rusaakkmods/dmg_boy_display/schematics/dmg_boy_display/dmg_boy_display.kicad_sch

## KiCad design schematics/dmg_boy_display/dmg_boy_display.kicad_sch (2025-08-26, an earlier design)

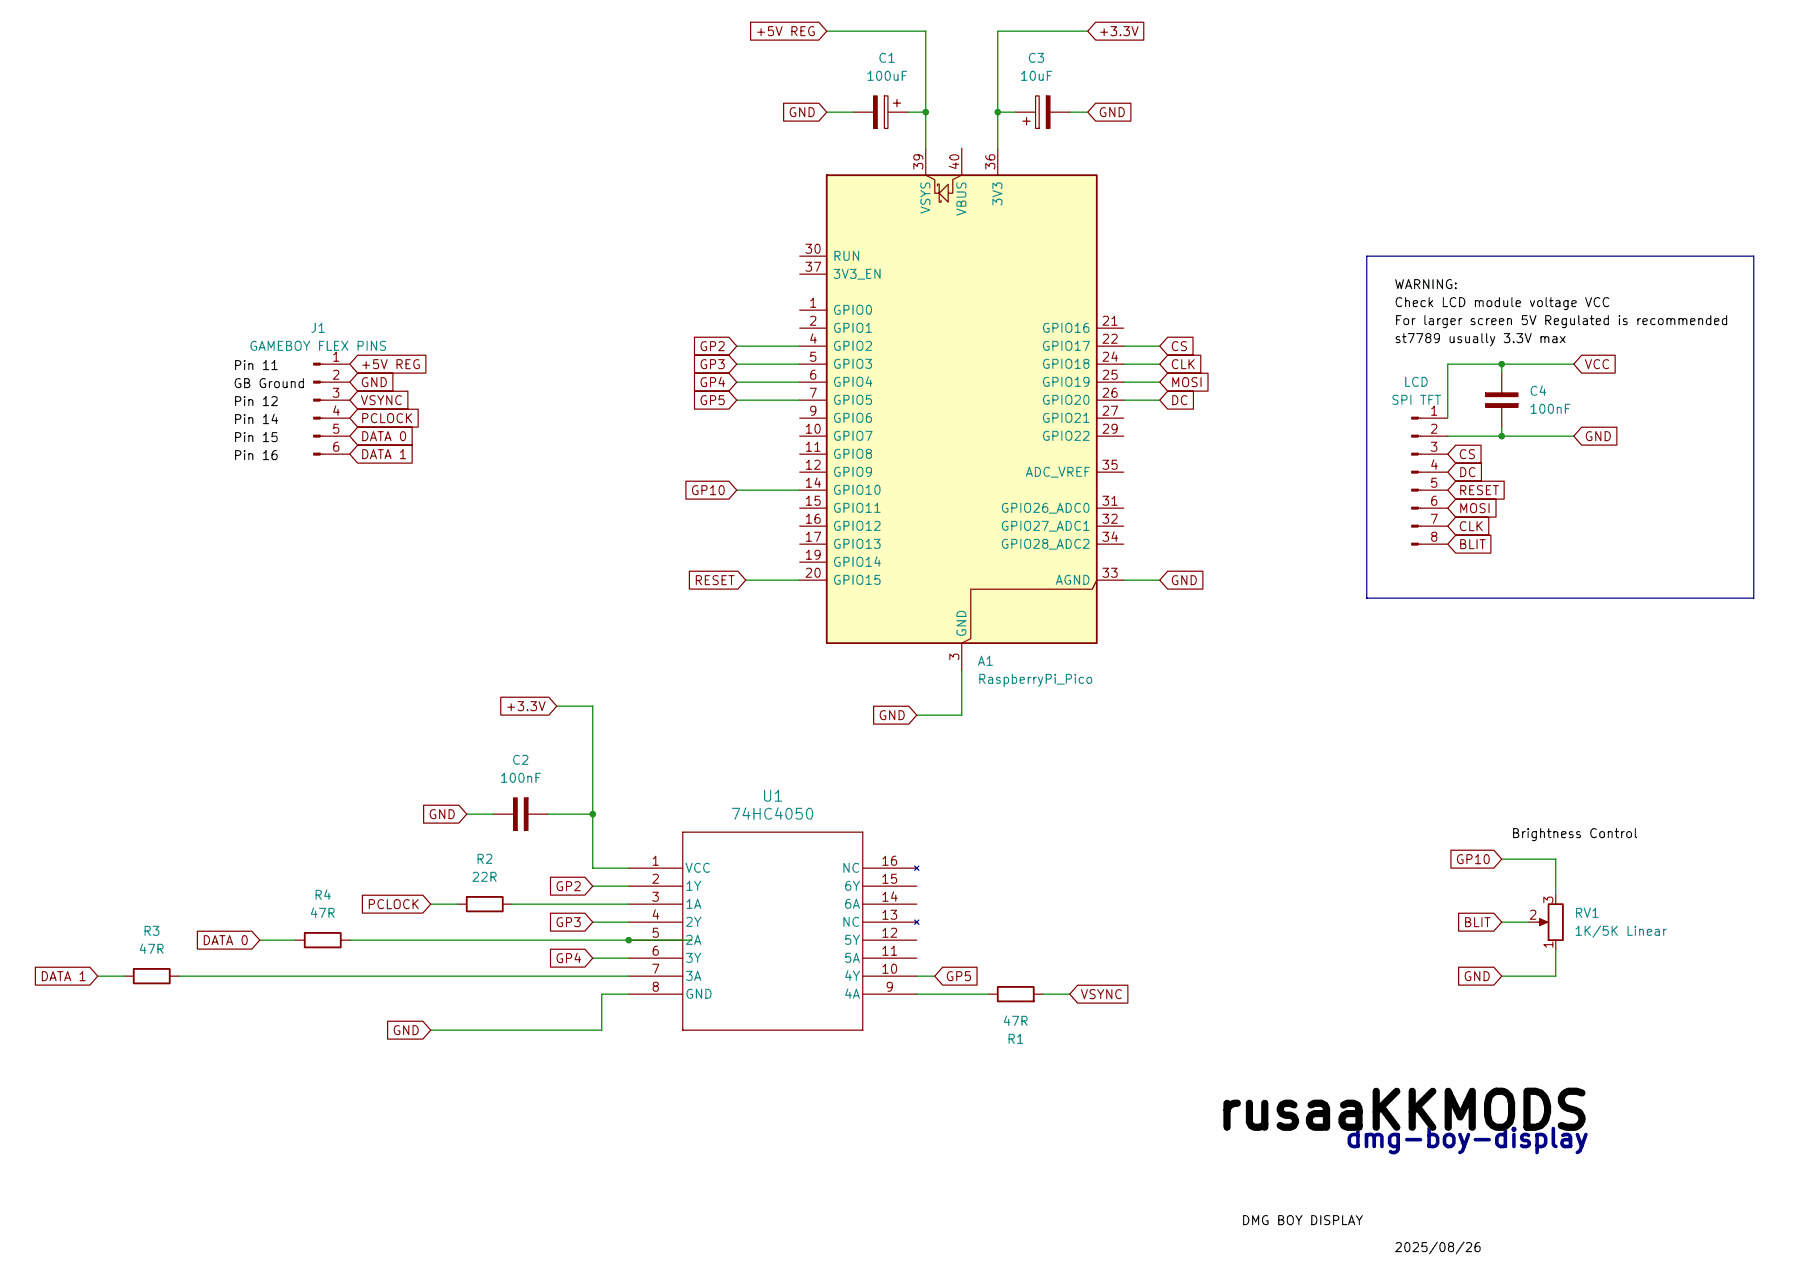
[picture p3: schematic dmg_boy_display.kicad_sch]

Parts:
A1: RaspberryPi_Pico; RaspberryPi_Pico_Common_Unspecified
C1: 100uF
C2, C4: 100nF
C3: 10uF
J1: GAMEBOY FLEX PINS
LCD: SPI TFT
R1, R3, R4: 47R
R2: 22R
RV1: 1K/5K Linear
U1: 74HC4050; N16_TEX

Connections:
+3.3V: A1.36 (3V3), C2.1, C3.1, U1.1 (VCC)
+5V REG: A1.39 (VSYS), C1.1, J1.1
BLIT: LCD.8, RV1.2
CLK: A1.24 (GPIO18), LCD.7
CS: A1.22 (GPIO17), LCD.3
DATA 0: J1.5, R4.2
DATA 1: J1.6, R3.2
DC: A1.26 (GPIO20), LCD.4
GND: A1.3 (GND), A1.8 (GND), A1.13 (GND), A1.18 (GND), A1.23 (GND), A1.28 (GND), A1.33 (AGND), A1.38 (GND), C1.2, C2.2, C3.2, C4.2, J1.2, LCD.2, RV1.1, U1.8 (GND)
GP2: A1.4 (GPIO2), U1.2 (1Y)
GP3: A1.5 (GPIO3), U1.4 (2Y)
GP4: A1.6 (GPIO4), U1.6 (3Y)
GP5: A1.7 (GPIO5), U1.10 (4Y)
GP10: A1.14 (GPIO10), RV1.3
MOSI: A1.25 (GPIO19), LCD.6
unnamed: R1.1, U1.9 (4A)
unnamed: R2.1, U1.3 (1A)
unnamed: R3.1, U1.7 (3A)
unnamed: R4.1, U1.5 (2A)
PCLOCK: J1.4, R2.2
RESET: A1.20 (GPIO15), LCD.5
VCC: C4.1, LCD.1
VSYNC: J1.3, R1.2

Notes on the sheet:
dmg-boy-display
